carrotIndustries/pluto/mech/image4566.png

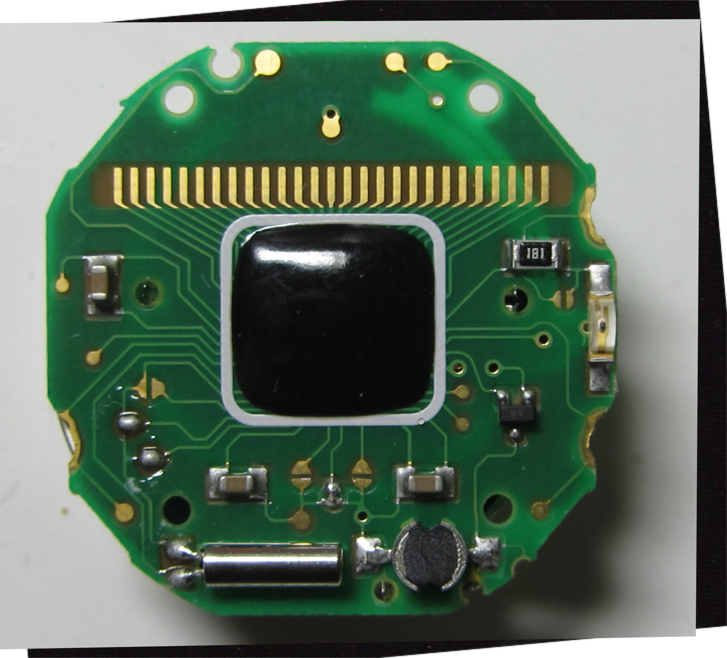
mech/image4566.png
